sndmax/Drumboy-Pro/02 Software/Drumboy-Pro-App-H723/Data/Design 540x960/Image_Lfo.bmp

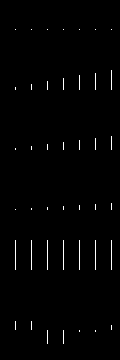
02 Software/Drumboy-Pro-App-H723/Data/Design 540x960/Image_Lfo.bmp
